billjuv/XIAO-LoRa-CO2-monitoring/Attachments/Photos/LoRa_Ant.jpeg

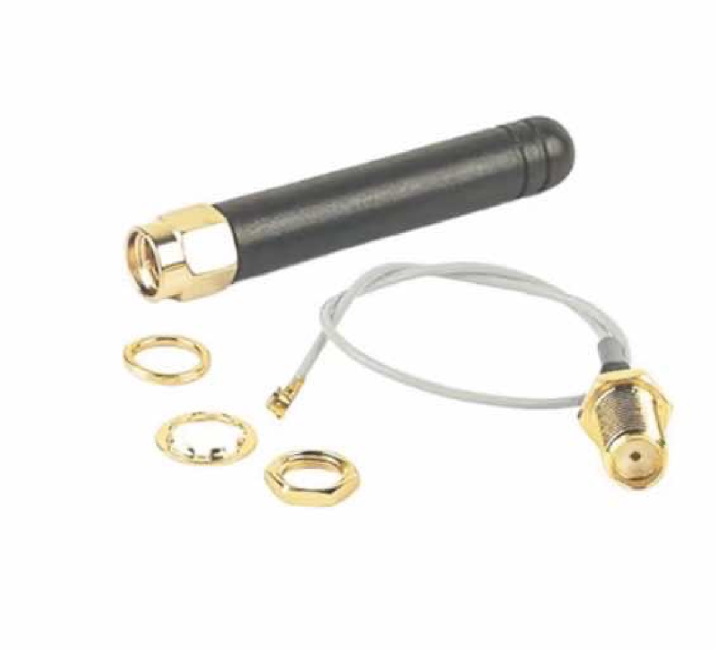
Attachments/Photos/LoRa_Ant.jpeg
