billjuv/XIAO-LoRa-CO2-monitoring/Attachments/Photos/USB_PwrCable.jpeg

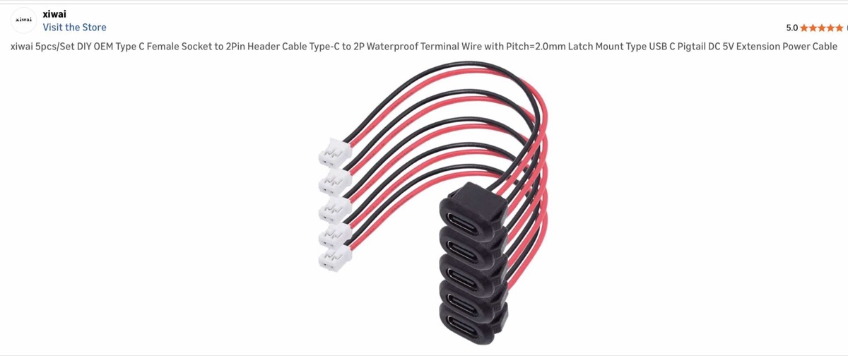
Attachments/Photos/USB_PwrCable.jpeg
