billjuv/XIAO-LoRa-CO2-monitoring/Attachments/Photos/XIAO_Enc1.jpeg

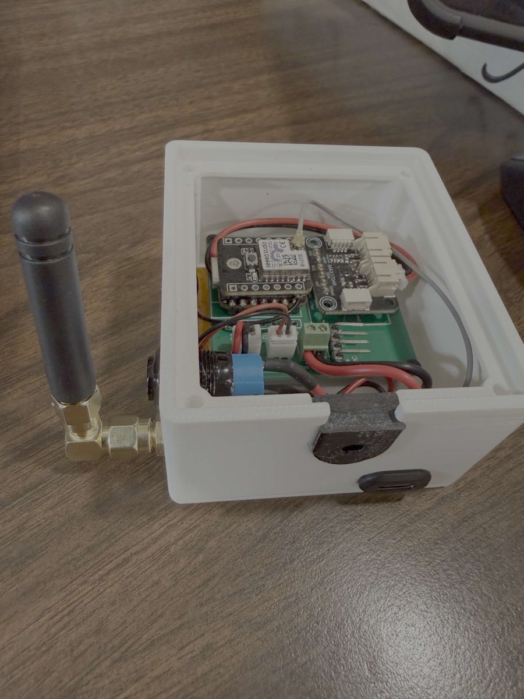
Attachments/Photos/XIAO_Enc1.jpeg
